VVoldemar/automatic_parking_system/photos/photo_2025-02-10_20-03-10.jpg

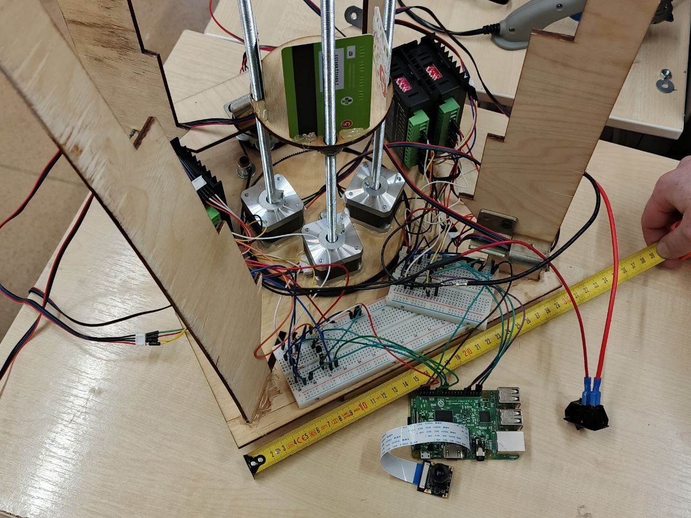
photos/photo_2025-02-10_20-03-10.jpg
