VVoldemar/automatic_parking_system/photos/photo_2025-02-10_20-04-09.jpg

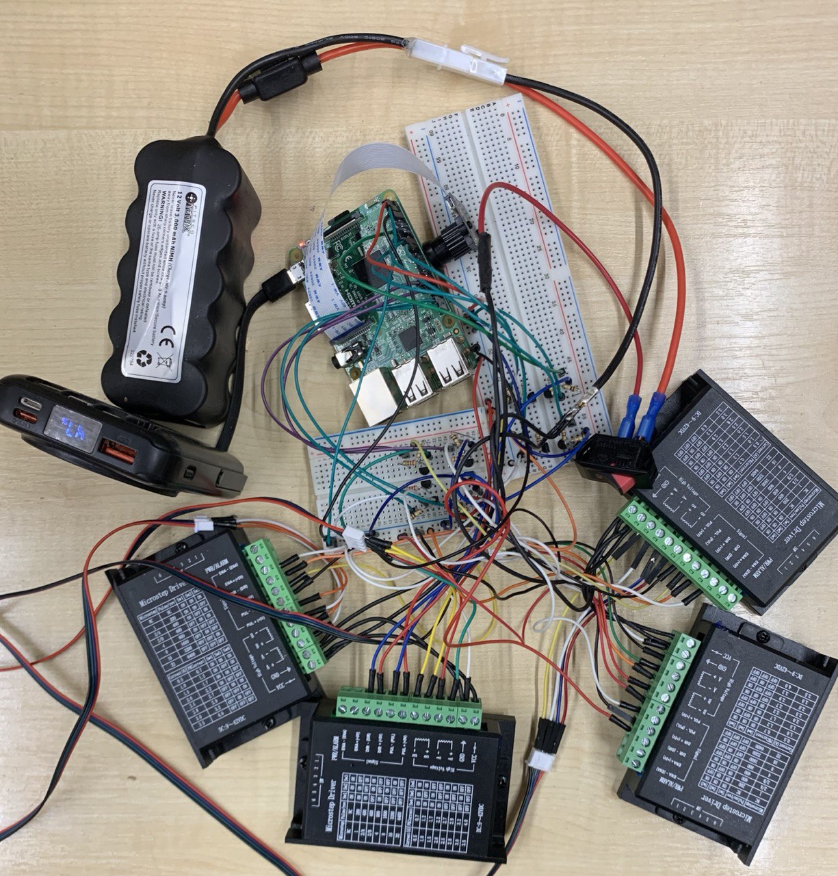
photos/photo_2025-02-10_20-04-09.jpg
