VVoldemar/automatic_parking_system/photos/photo_2025-02-10_20-06-13.jpg

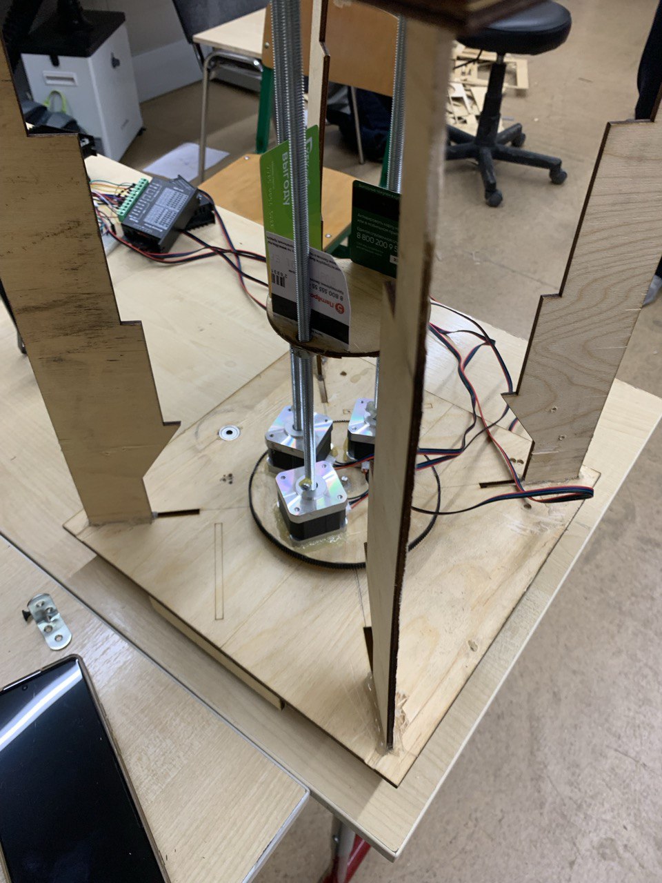
photos/photo_2025-02-10_20-06-13.jpg
