VVoldemar/automatic_parking_system/photos/photo_2025-02-10_22-27-32 (2).jpg

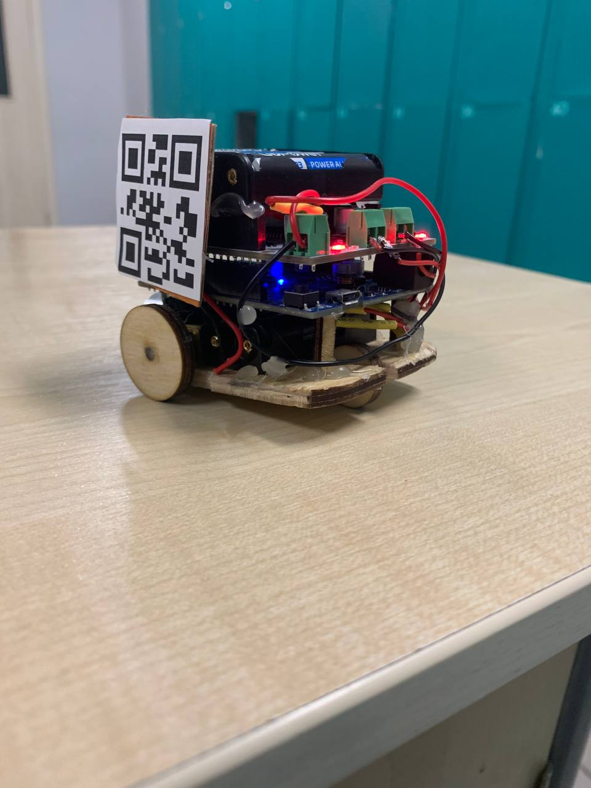
photos/photo_2025-02-10_22-27-32 (2).jpg
