VVoldemar/automatic_parking_system/photos/photo_2025-02-10_22-27-34.jpg

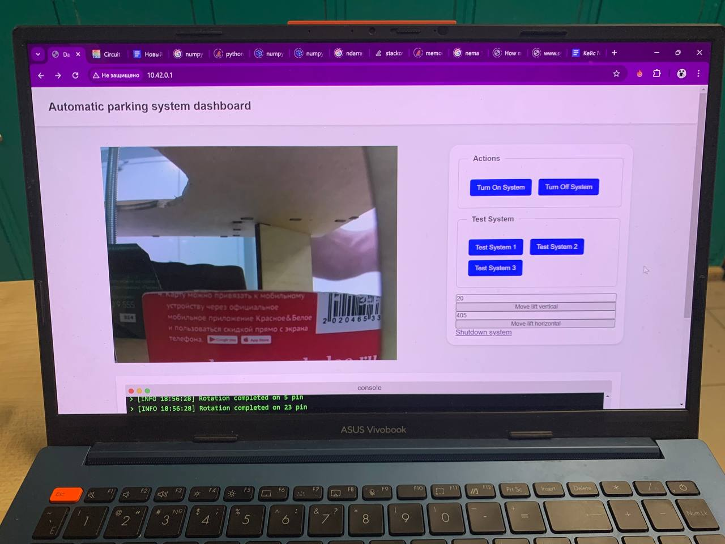
photos/photo_2025-02-10_22-27-34.jpg
